CarbonComputers/PiBerry/blueprint/3.png

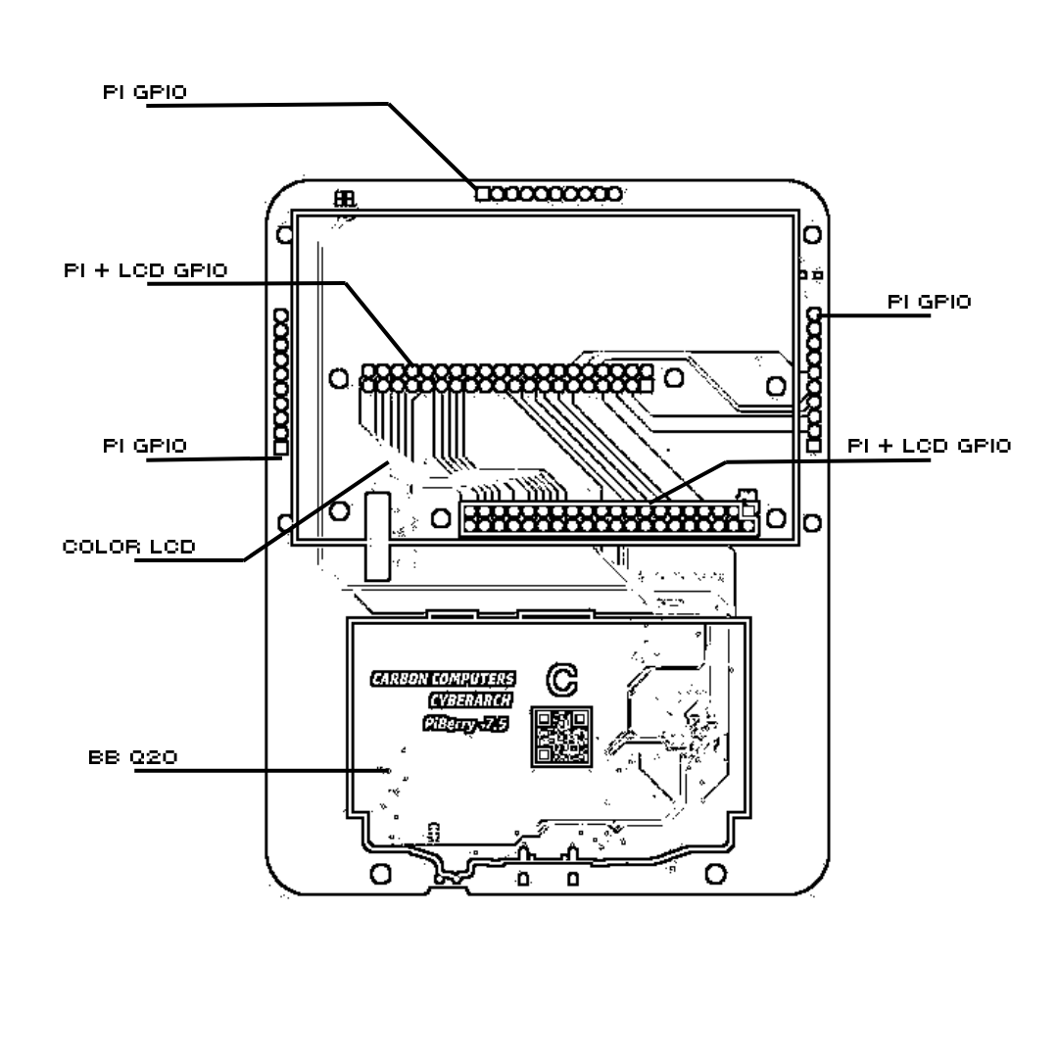
blueprint/3.png
