CarbonComputers/PiBerry/blueprint/4.png

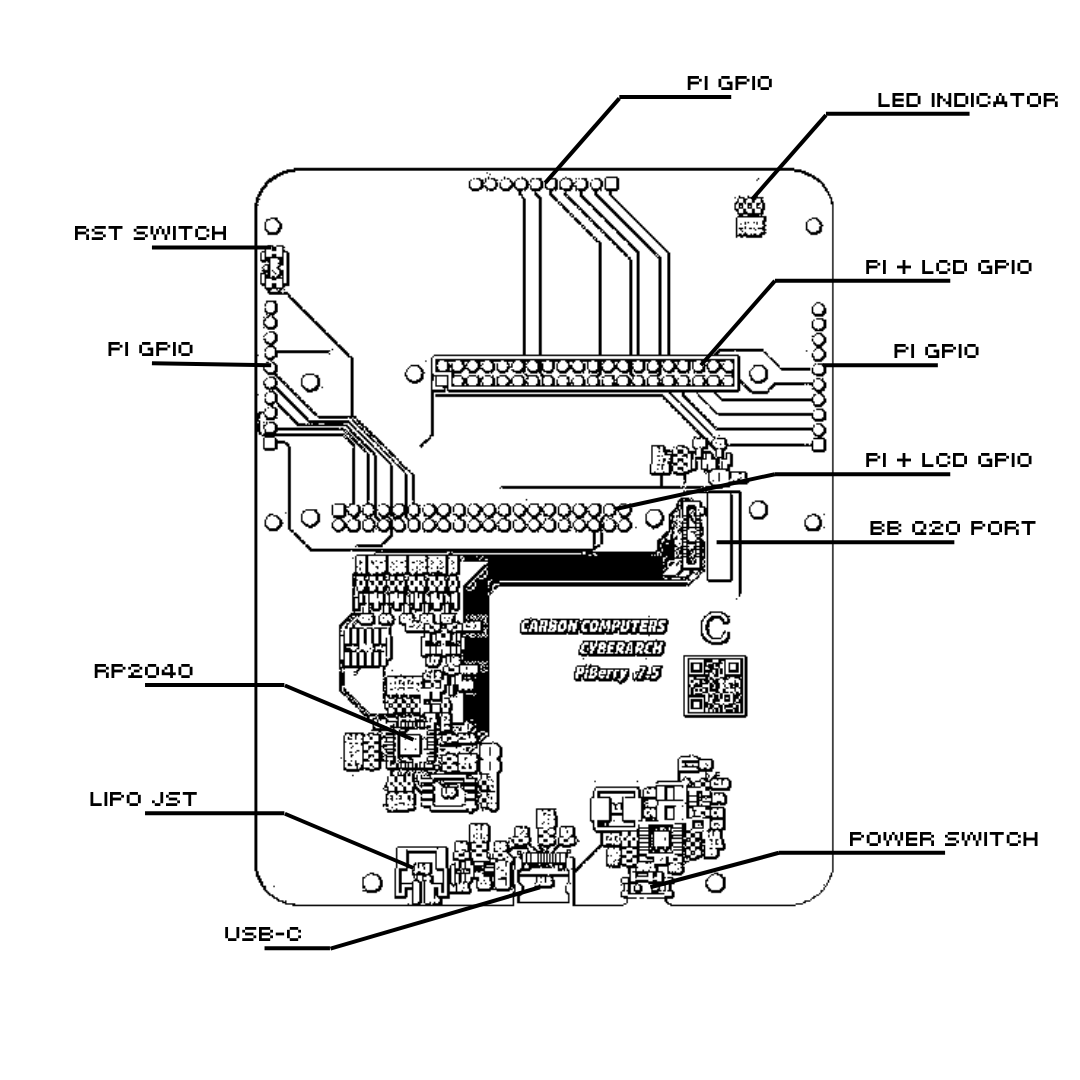
blueprint/4.png
