CarbonComputers/PiBerry/img/v8.0_retro.jpg

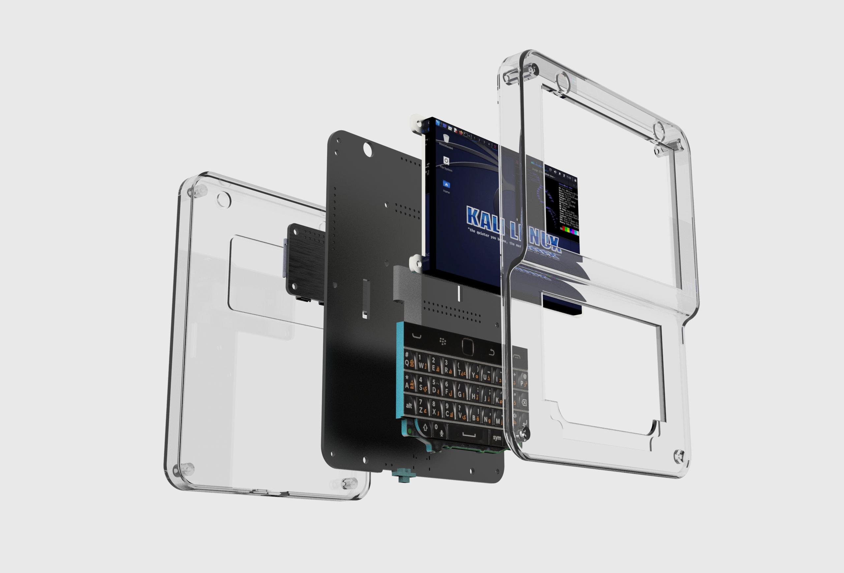
img/v8.0_retro.jpg
